circuitrocks/SensoWing/Pictures/1.PNG

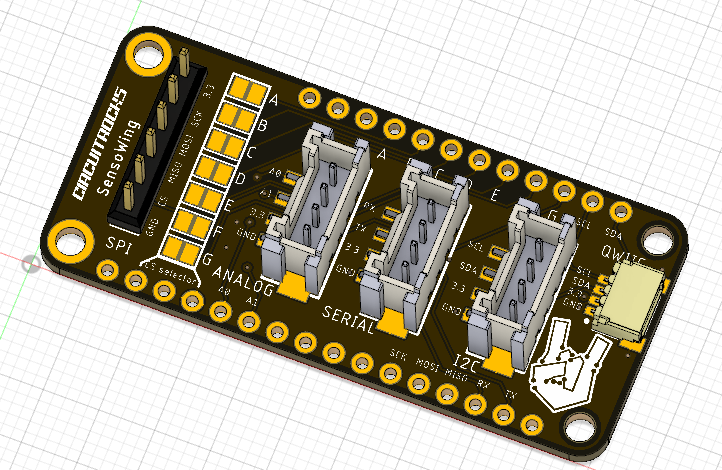
Pictures/1.PNG
