circuitrocks/SensoWing/Pictures/Grove Analog.PNG

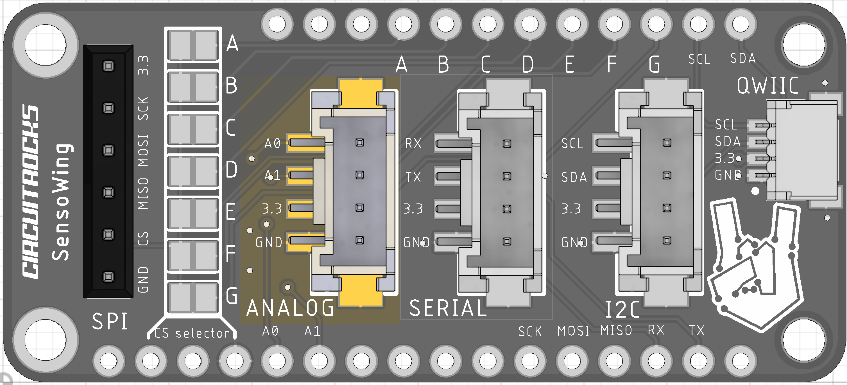
Pictures/Grove Analog.PNG
